Llcoolsouder/final-project-modulin/Code/EncoderLib.h

/*
*	This is a library of fuctions to interact with encoders on
*	the Modulin using the MSP430FR2311.
*
*	The applications of this library are specific
*	to the Modulin project for Rowan University's "Introduction to
*	Embedded Systems." As such, this is in no way a comprehensive or
*	universal library for all projects using the encoders.
*
*	Lonnie L. Souder II
*	Undergraduate
*	Rowan University,
*	Department of Electrical & Computer Engineering
*	11/25/2017
*/

#include <msp430.h>
